ednieuw/Arduino-ESP32-Nano-Wordclock/PCB/Nano-ESP32-V04.jpg

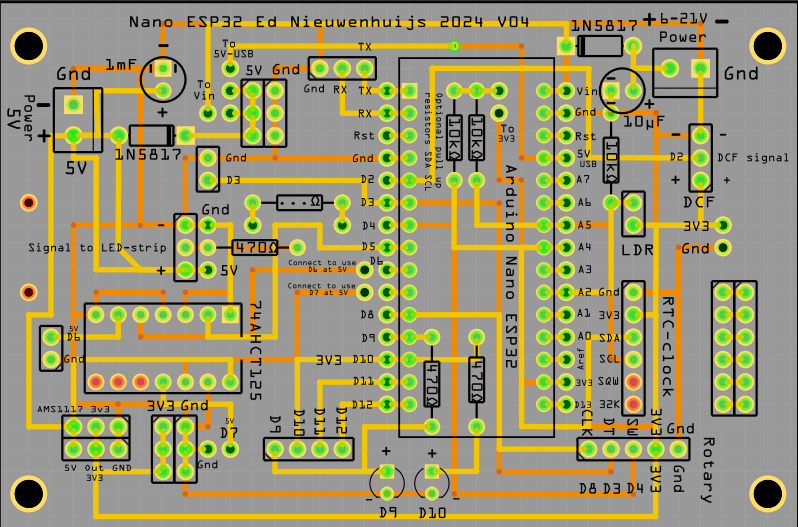
PCB/Nano-ESP32-V04.jpg
