ednieuw/Arduino-ESP32-Nano-Wordclock/PCB/NanoESP32-V04-3D.jpg

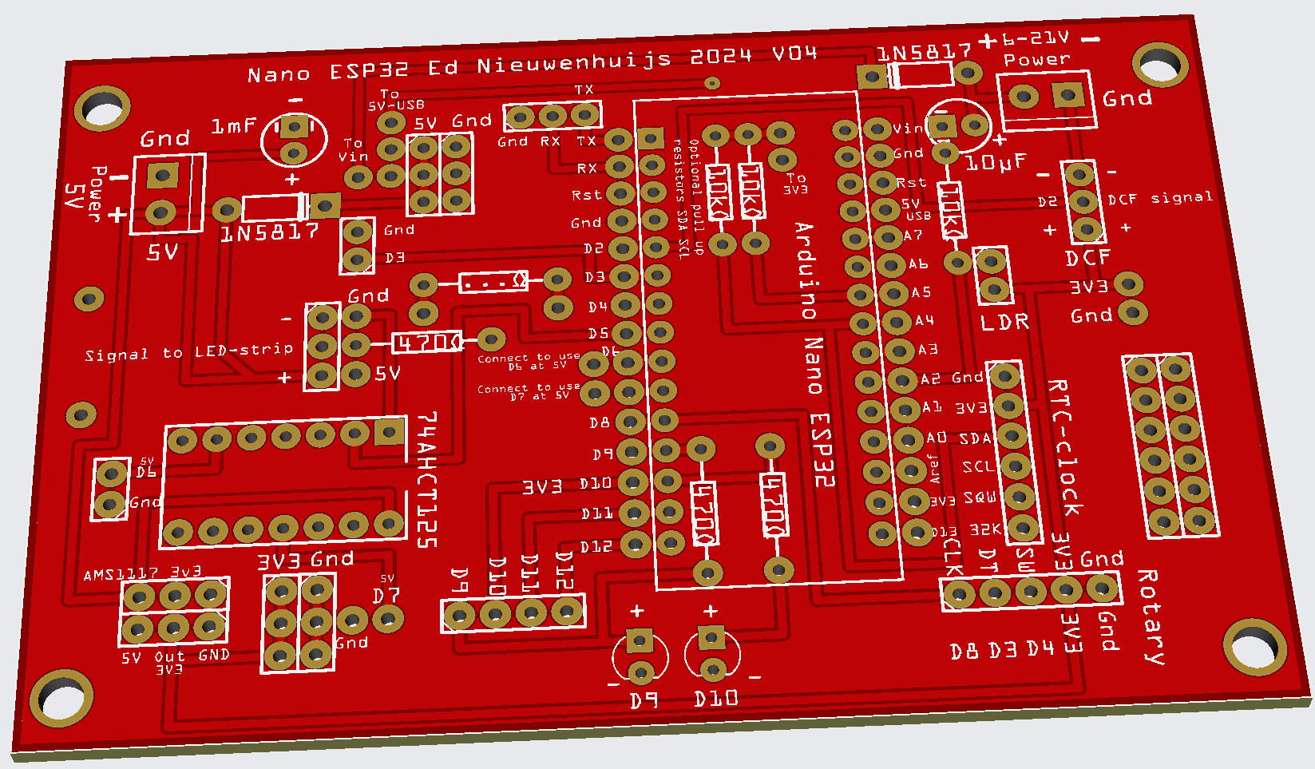
PCB/NanoESP32-V04-3D.jpg
