ednieuw/Arduino-ESP32-Nano-Wordclock/Pics/IMG_1467.JPG

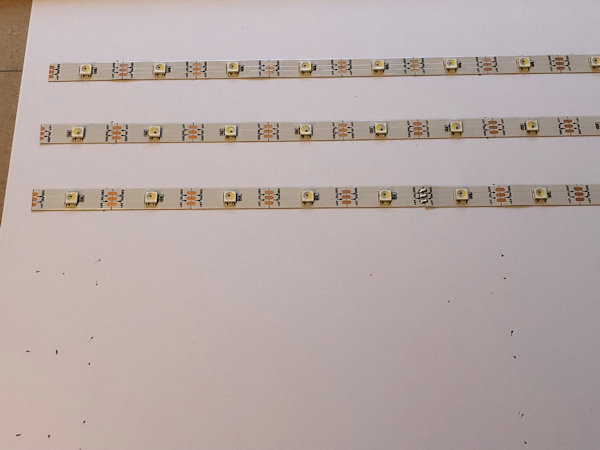
Pics/IMG_1467.JPG
