ednieuw/Arduino-ESP32-Nano-Wordclock/Pics/IMG_1469.JPG

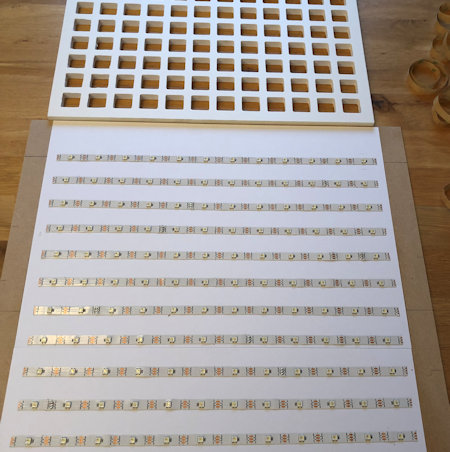
Pics/IMG_1469.JPG
