ednieuw/Arduino-ESP32-Nano-Wordclock/Pics/IMG_1471.JPG

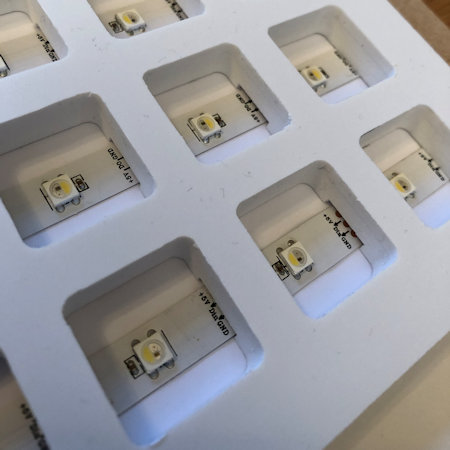
Pics/IMG_1471.JPG
