ednieuw/Arduino-ESP32-Nano-Wordclock/Pics/IMG_5384.JPG

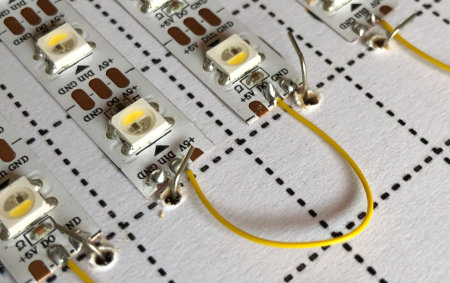
Pics/IMG_5384.JPG
