ednieuw/Arduino-ESP32-Nano-Wordclock/Pics/Spacerplaat.jpg

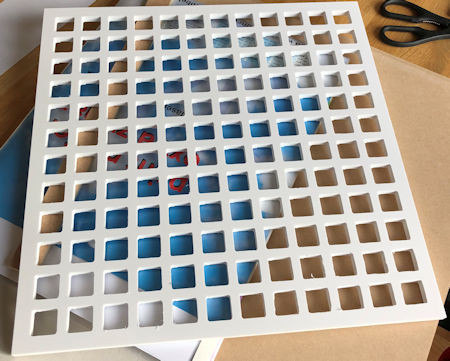
Pics/Spacerplaat.jpg
