ednieuw/Arduino-ESP32-Nano-Wordclock/Pics/Terminal450.jpg

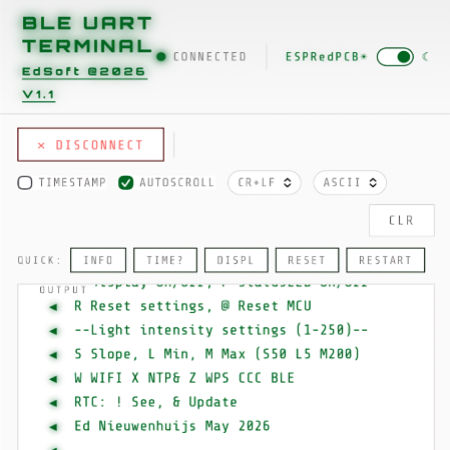
Pics/Terminal450.jpg
