ednieuw/Arduino-ESP32-Nano-Wordclock/Pics/V200BLEserialMenu.jpg

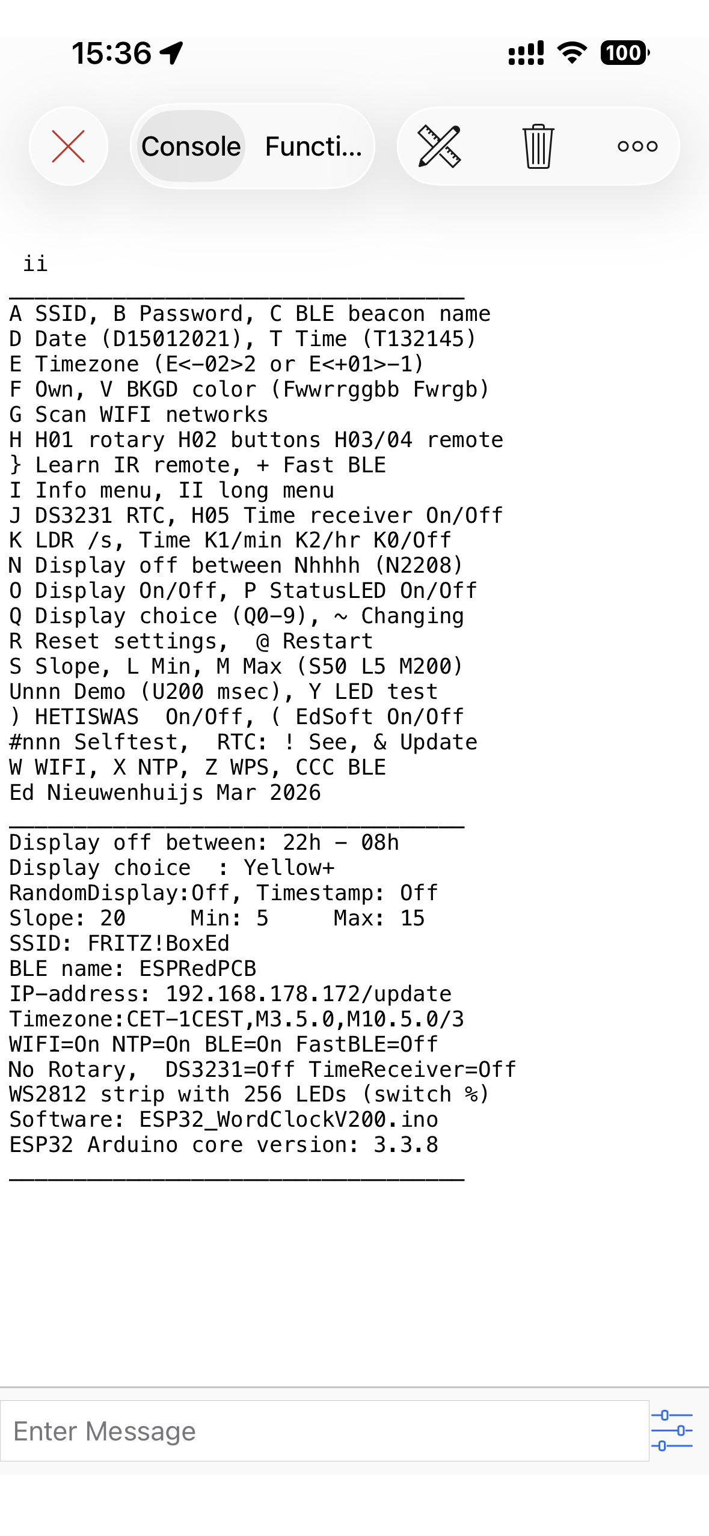
Pics/V200BLEserialMenu.jpg
