ednieuw/Arduino-ESP32-Nano-Wordclock/WordPlateFrontCovers/Duits_08sep2018_50x50cm.jpg

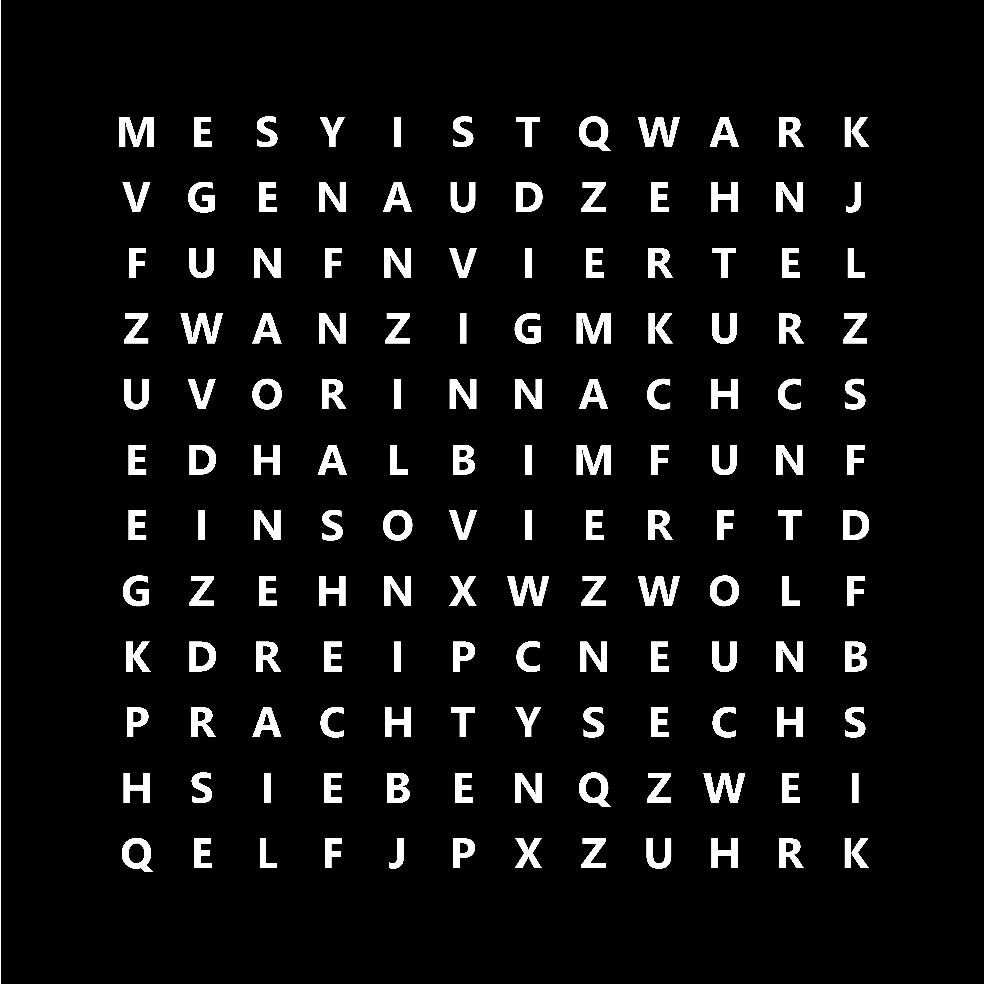
WordPlateFrontCovers/Duits_08sep2018_50x50cm.jpg
