ednieuw/Arduino-ESP32-Nano-Wordclock/WordPlateFrontCovers/Engels_08sep2018_50x50cm.jpg

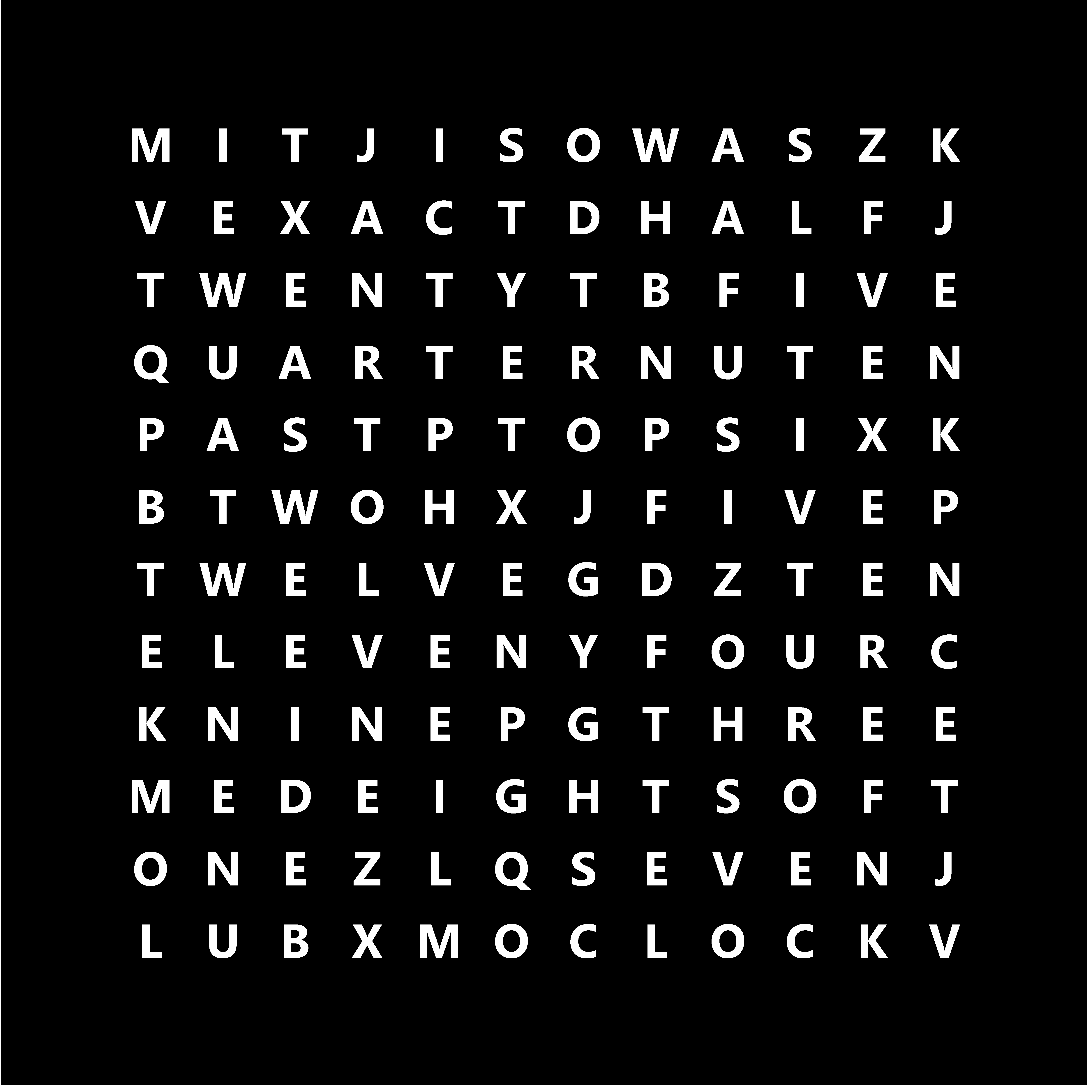
WordPlateFrontCovers/Engels_08sep2018_50x50cm.jpg
