ednieuw/Arduino-ESP32-Nano-Wordclock/WordPlateFrontCovers/Frans08sep2018_50x50cm.jpg

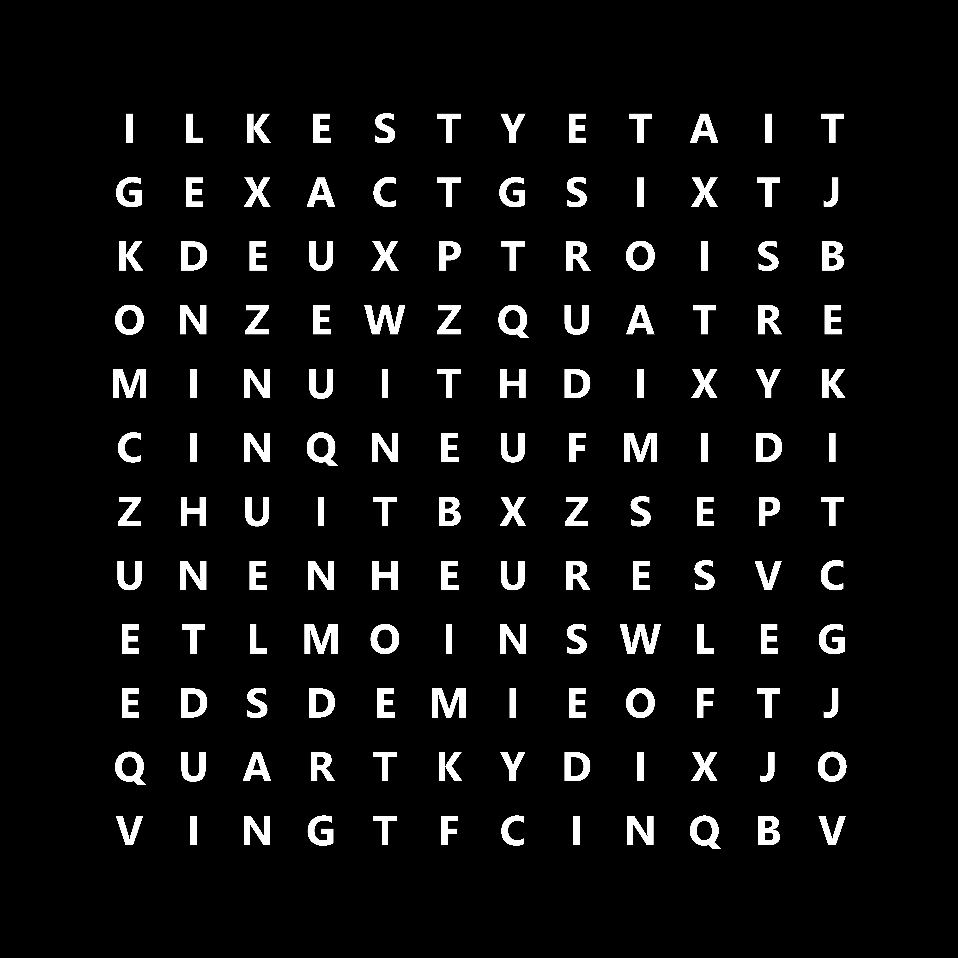
WordPlateFrontCovers/Frans08sep2018_50x50cm.jpg
