ednieuw/Arduino-ESP32-Nano-Wordclock/WordPlateFrontCovers/Nederlands_08sep2018_50x50cm.jpg

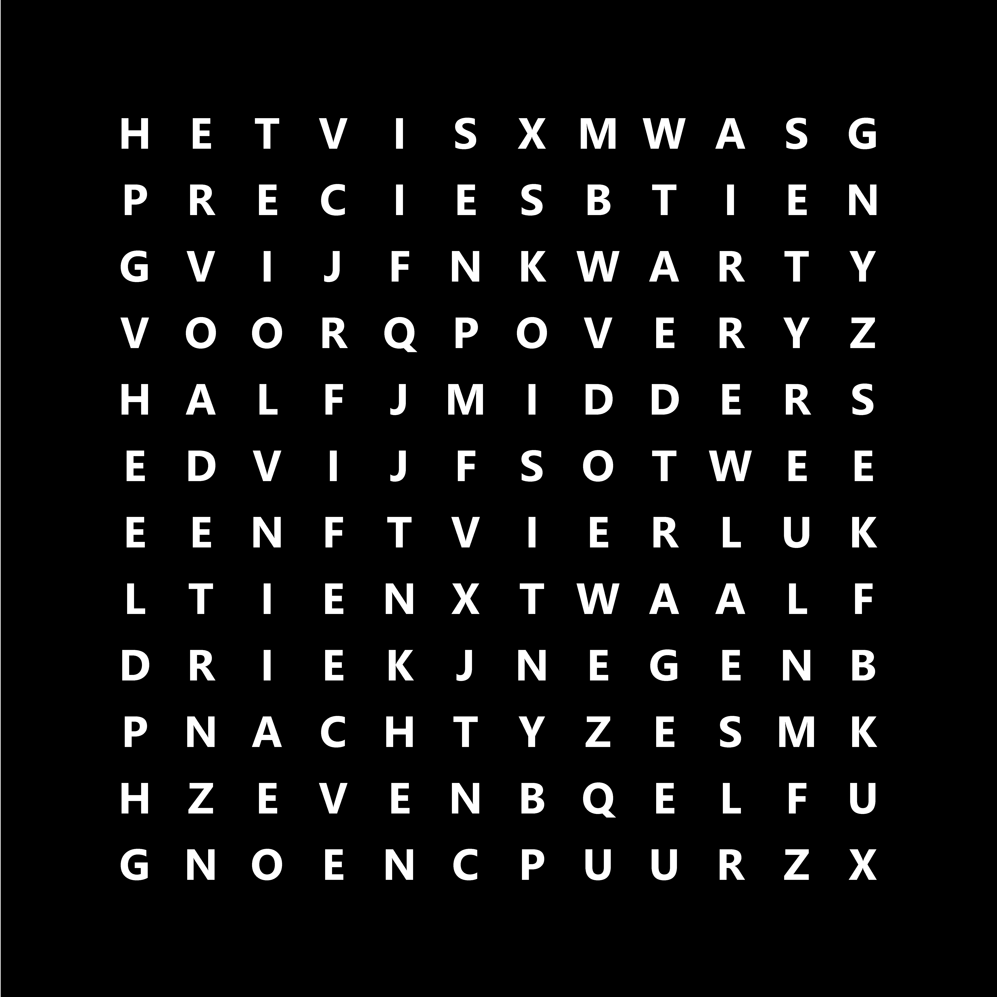
WordPlateFrontCovers/Nederlands_08sep2018_50x50cm.jpg
