ednieuw/Arduino-ESP32-Nano-Wordclock/WordPlateFrontCovers/Viertalen-AlleLetters-23okt2018_100x100cm.jpg

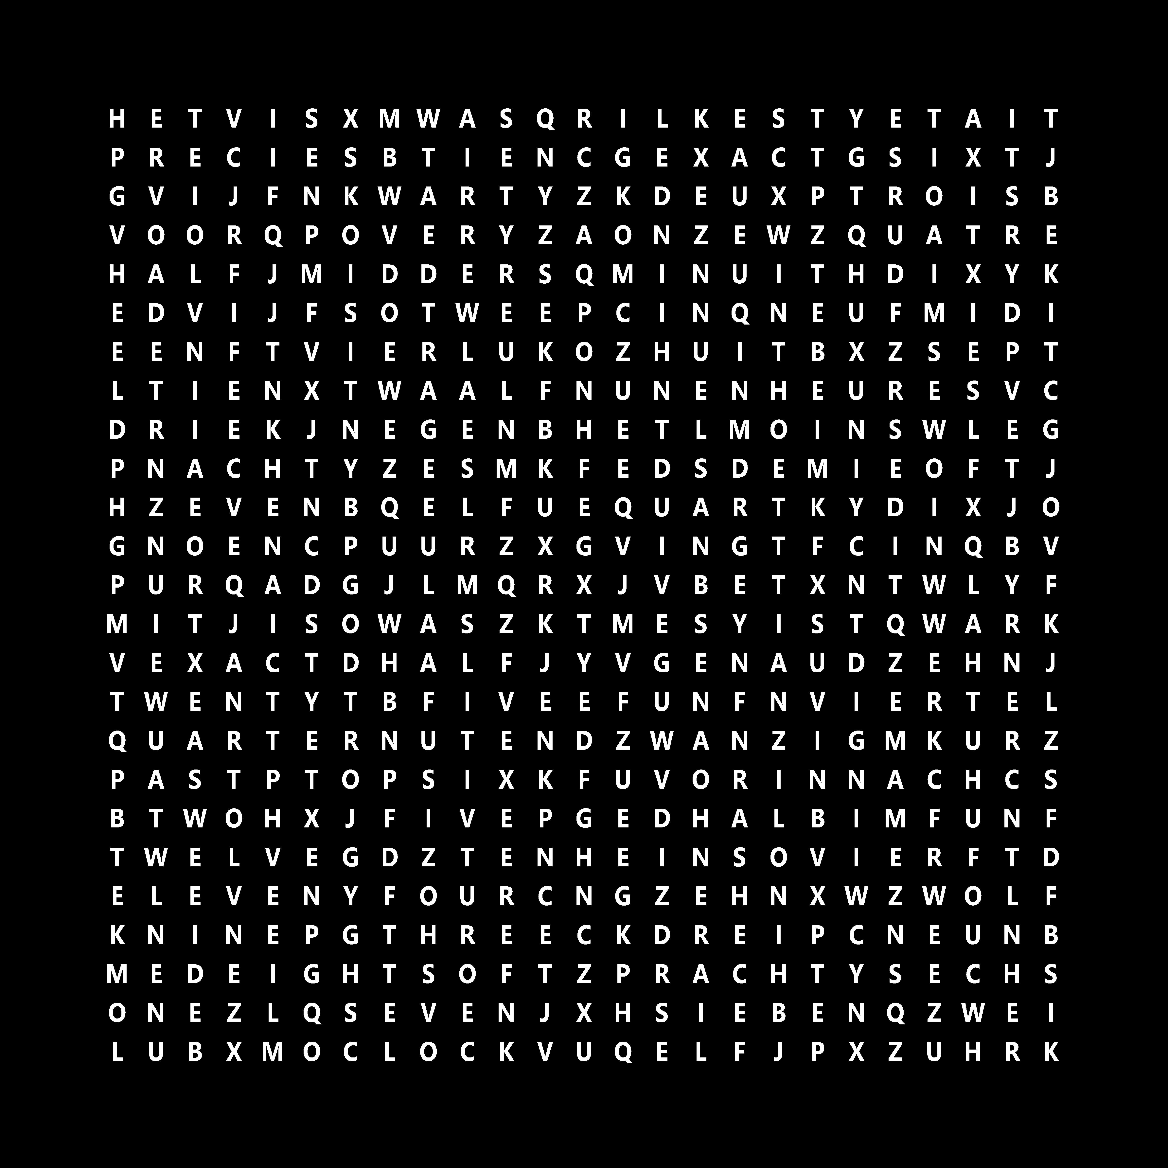
WordPlateFrontCovers/Viertalen-AlleLetters-23okt2018_100x100cm.jpg
