ednieuw/Arduino-ESP32-Nano-Wordclock/Manual-Instructions/Manual_ArduinoESP32Nano_files/image011.png

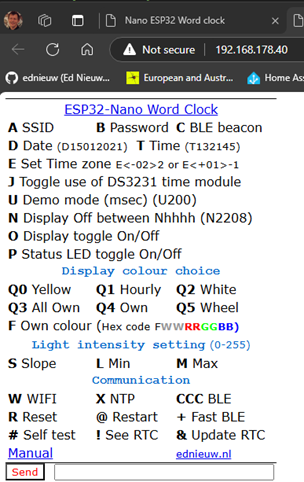
Manual-Instructions/Manual_ArduinoESP32Nano_files/image011.png
